sparkfun/SparkFun_IM19_IMU_Breakout/Hardware/Dimensions.png

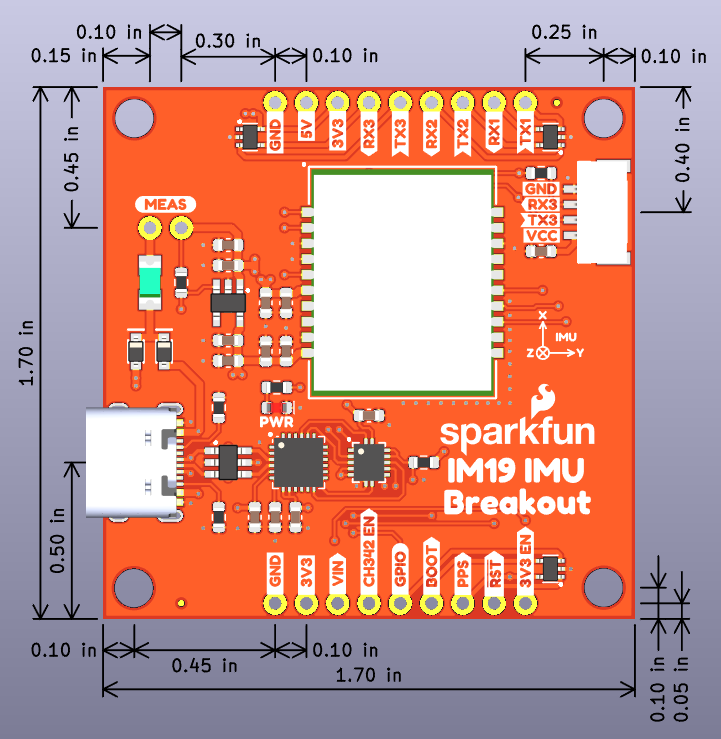
Hardware/Dimensions.png
