sparkfun/SparkFun_IM19_IMU_Breakout/static/board_files/dimensions.png

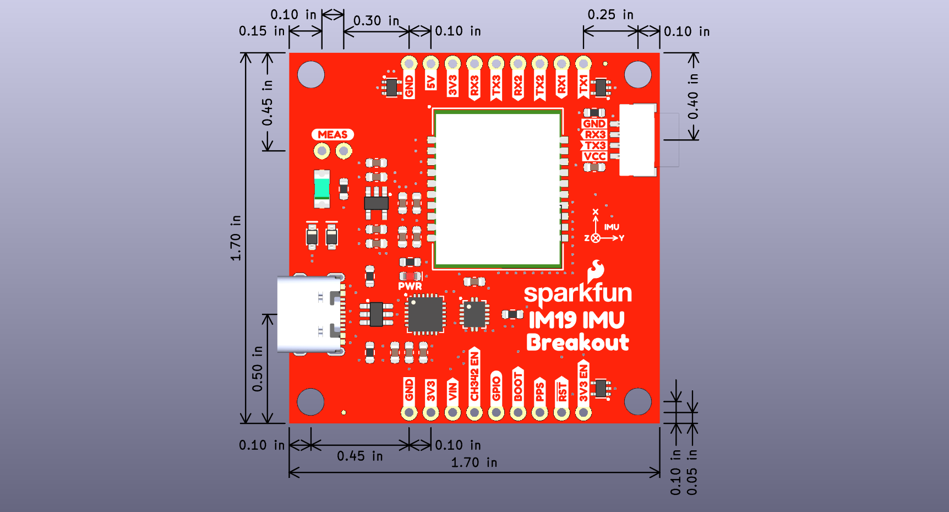
static/board_files/dimensions.png
