sparkfun/SparkFun_IM19_IMU_Breakout/static/img/hookup_guide/assembly-headers.jpg

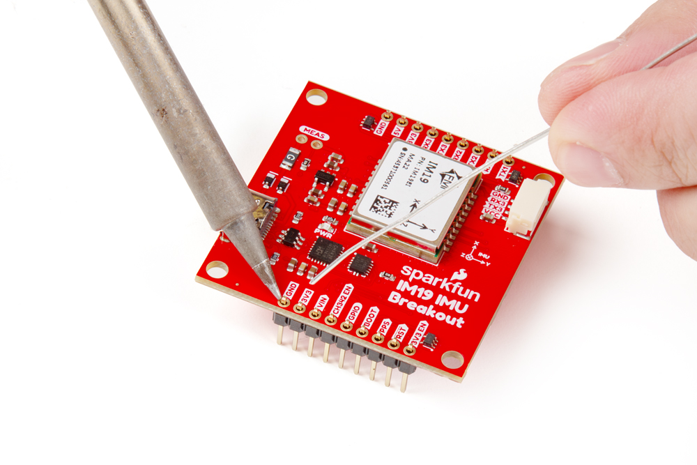
static/img/hookup_guide/assembly-headers.jpg
