sparkfun/SparkFun_IM19_IMU_Breakout/static/img/hookup_guide/assembly-usb.jpg

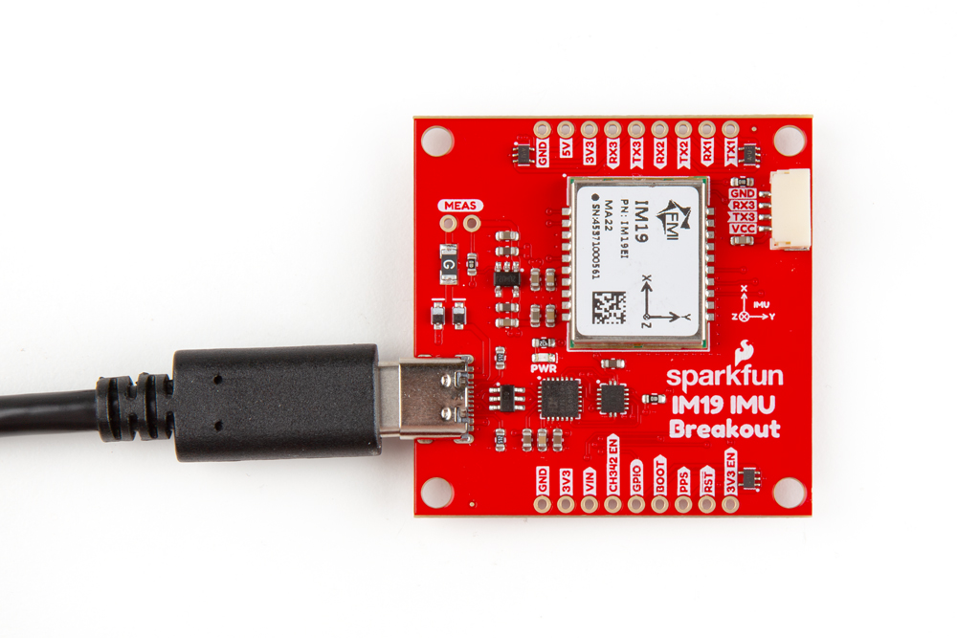
static/img/hookup_guide/assembly-usb.jpg
