sparkfun/SparkFun_IM19_IMU_Breakout/static/img/hookup_guide/boot_reset.png

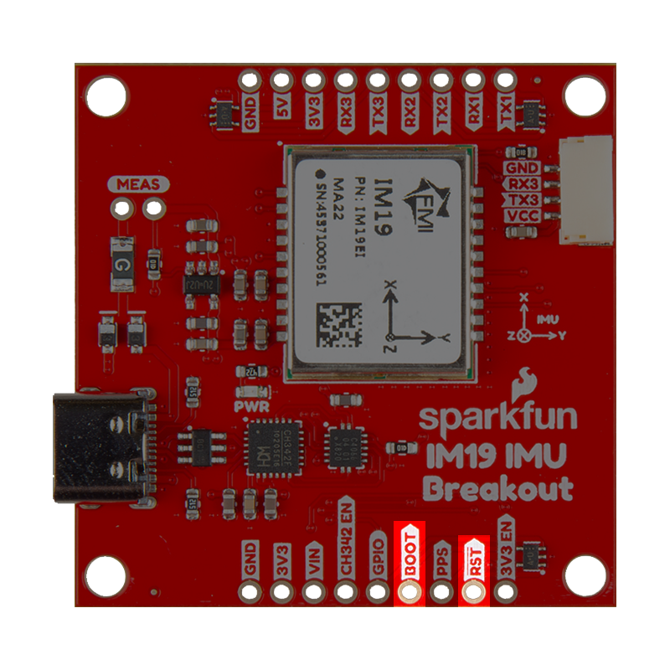
static/img/hookup_guide/boot_reset.png
