sparkfun/SparkFun_IM19_IMU_Breakout/static/img/hookup_guide/im19-height.png

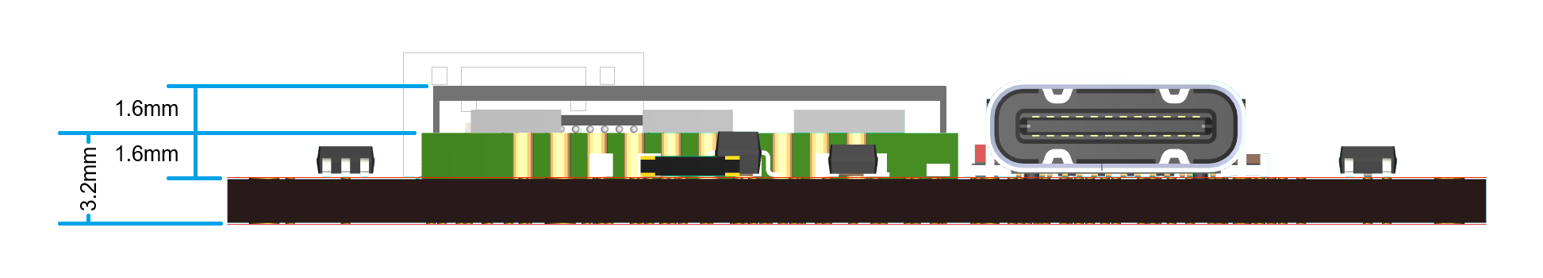
static/img/hookup_guide/im19-height.png
