sparkfun/SparkFun_IM19_IMU_Breakout/static/img/hookup_guide/im19-origin_bottom.png

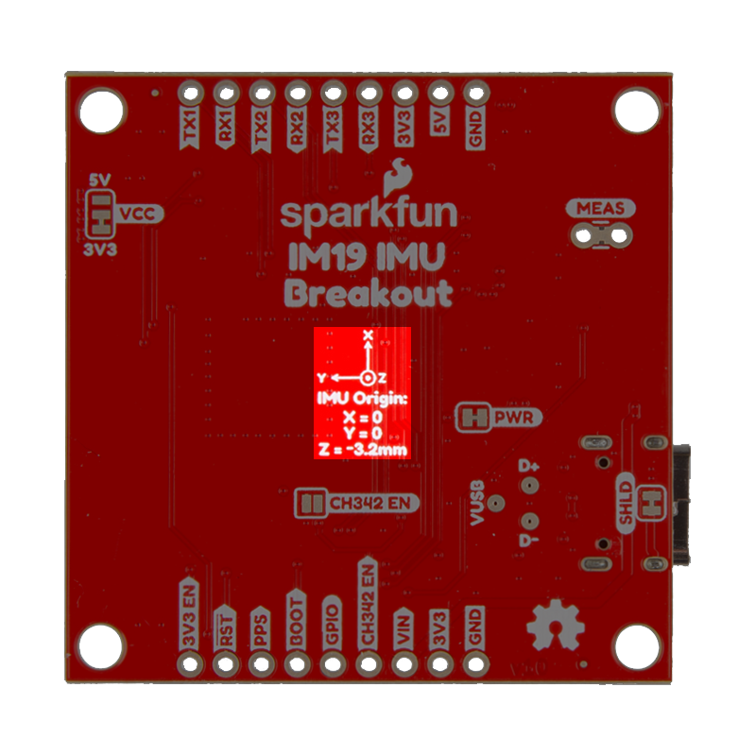
static/img/hookup_guide/im19-origin_bottom.png
