sparkfun/SparkFun_IM19_IMU_Breakout/static/img/hookup_guide/im19.png

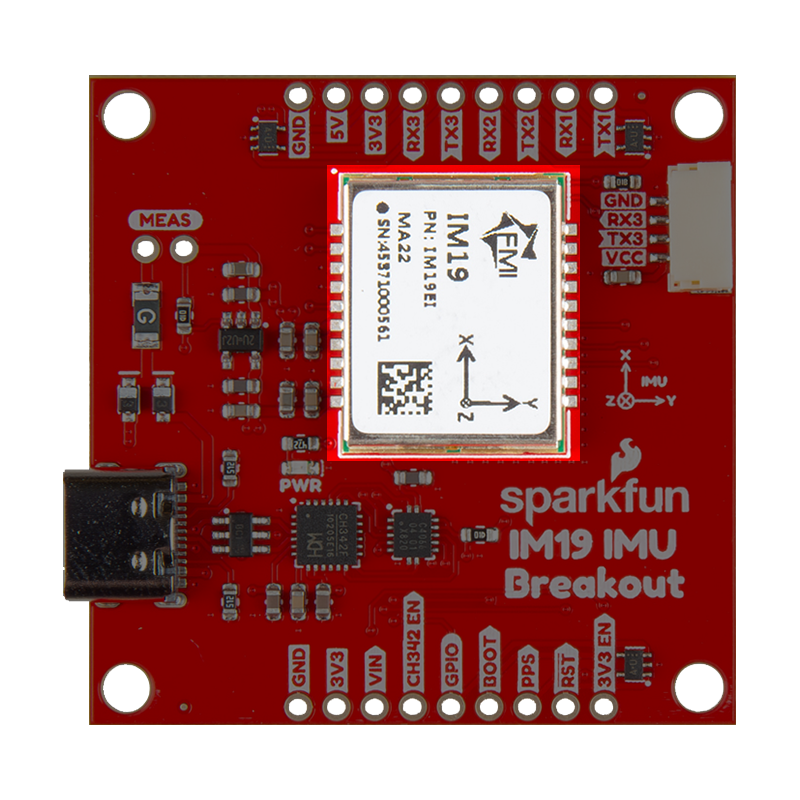
static/img/hookup_guide/im19.png
