sparkfun/SparkFun_IM19_IMU_Breakout/static/img/hookup_guide/integration-gnss.png

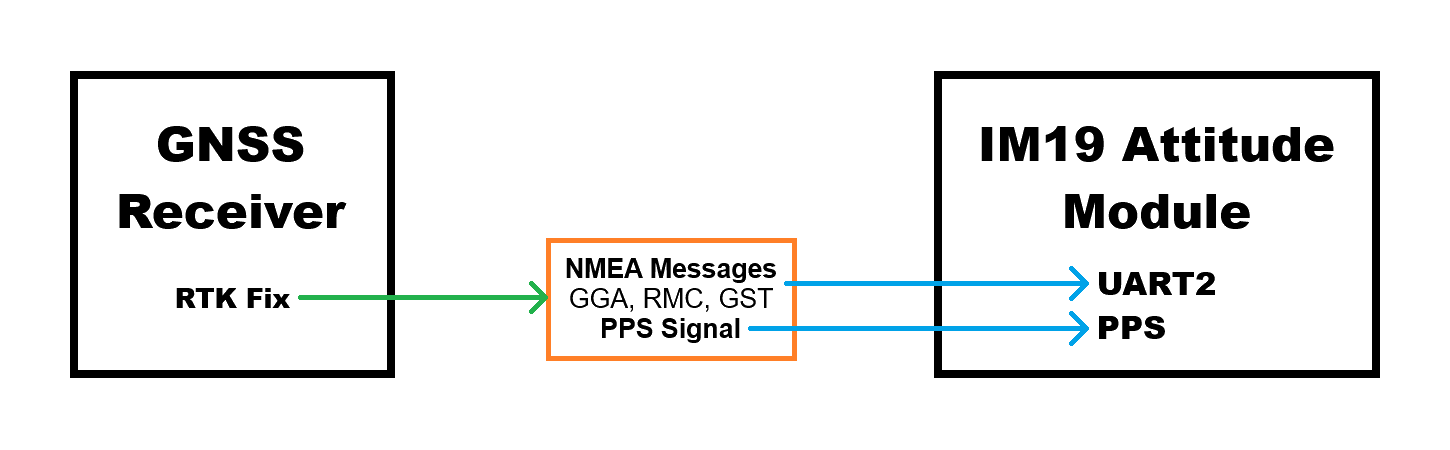
static/img/hookup_guide/integration-gnss.png
