sparkfun/SparkFun_IM19_IMU_Breakout/static/img/hookup_guide/integration-host.png

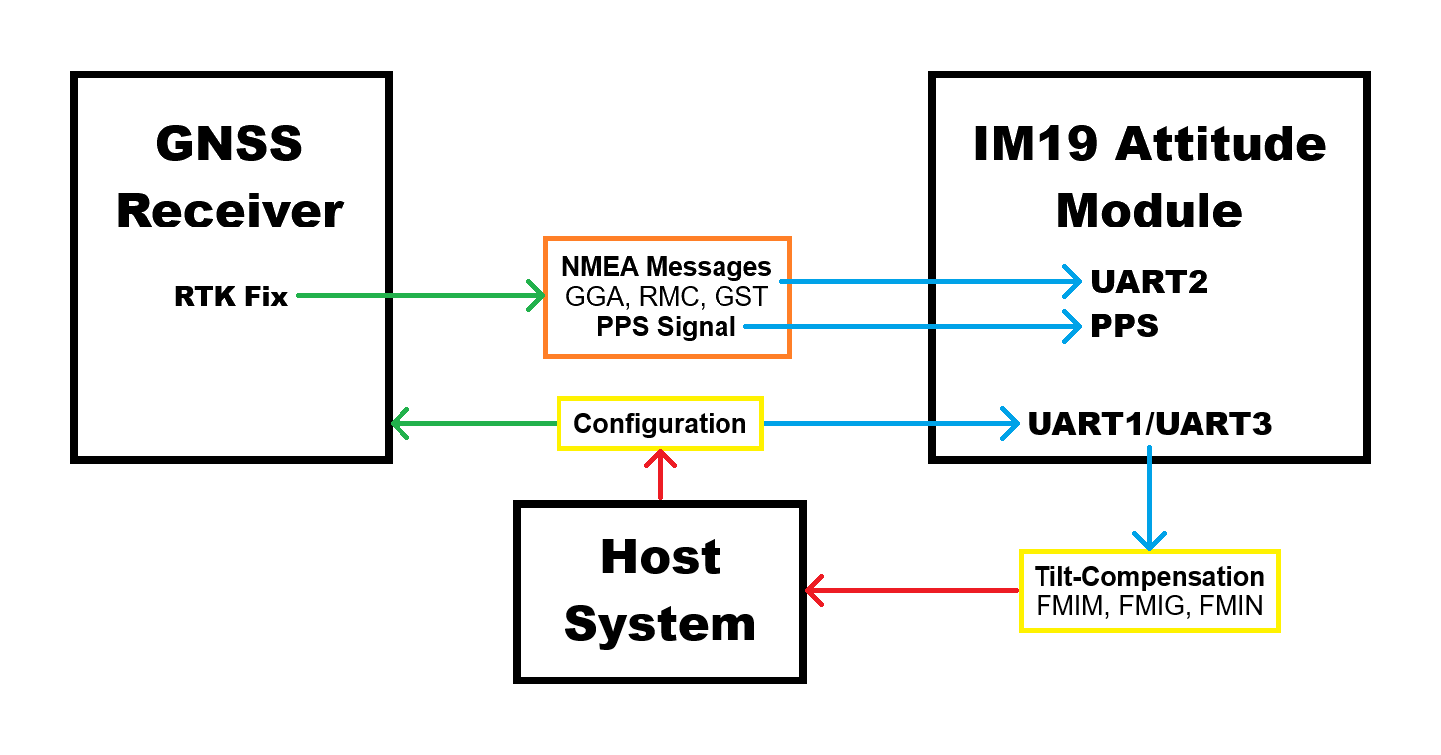
static/img/hookup_guide/integration-host.png
