sparkfun/SparkFun_IM19_IMU_Breakout/static/img/hookup_guide/jst-4_pin.png

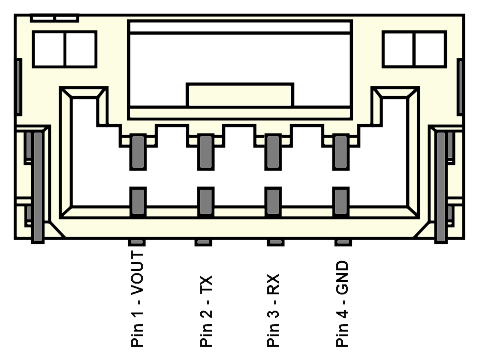
static/img/hookup_guide/jst-4_pin.png
