sparkfun/SparkFun_IM19_IMU_Breakout/static/img/hookup_guide/power_connections.png

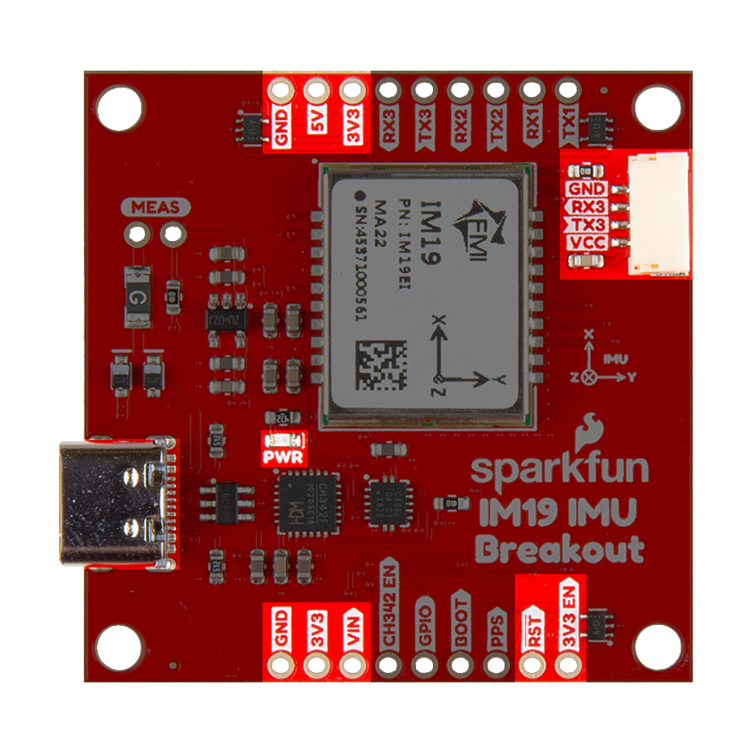
static/img/hookup_guide/power_connections.png
