sparkfun/SparkFun_IM19_IMU_Breakout/static/img/hookup_guide/pygpsclient-uart_settings-small.png

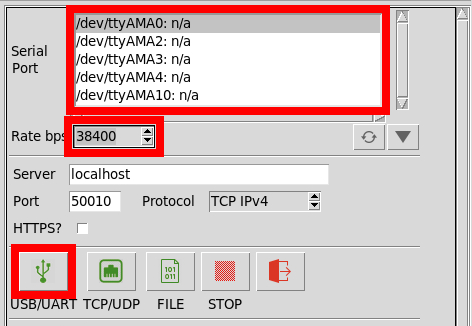
static/img/hookup_guide/pygpsclient-uart_settings-small.png
