sparkfun/SparkFun_IM19_IMU_Breakout/static/img/hookup_guide/uart-ch342.png

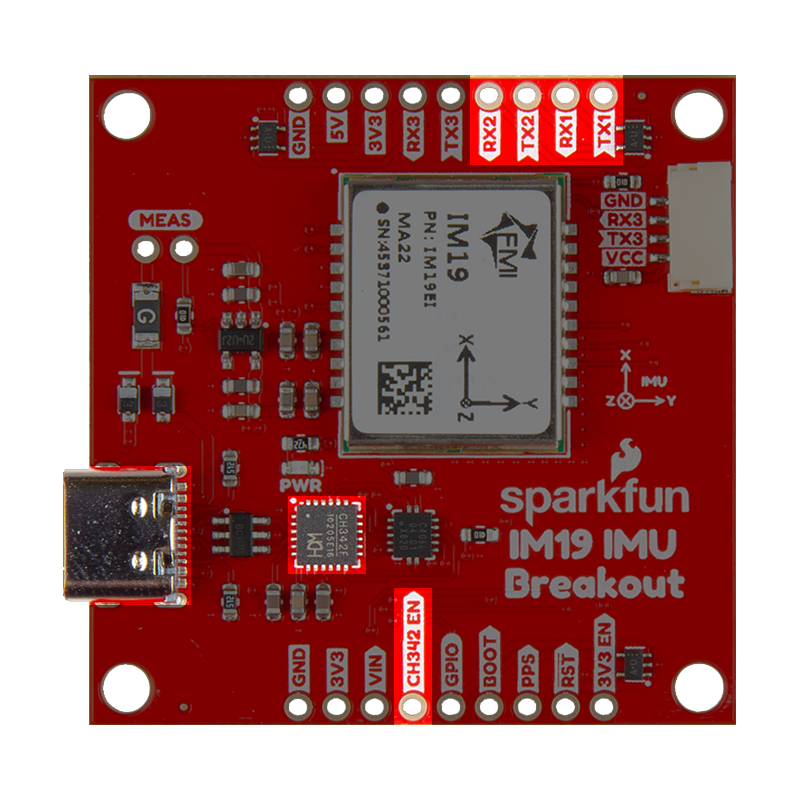
static/img/hookup_guide/uart-ch342.png
