sparkfun/SparkFun_IM19_IMU_Breakout/static/img/hookup_guide/vector_points.png

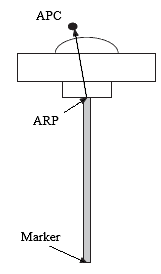
static/img/hookup_guide/vector_points.png
